martin-wagner/TuningIndicator_em34/sim/opamp-rect-bridge.asc

C1: cap; 1000µ
C2: cap; 10µ
D1: schottky; BAT54
D2: schottky; BAT54
D3: schottky; BAT54
D4: schottky; BAT54
R1: res; 10k
R2: res; 2.2Meg
R3: res; 15Meg
U1: UniversalOpamp2
V1: voltage; SINE(0 8 50 0 0 0 1000)
V2: voltage; 10
Named nets: 0, v_op, v_uc
.tran 1s
